sgmk/Parametrized-RAKO-Box/STL-Ready4Print/V5/midSize/midSize_V5_box.stl

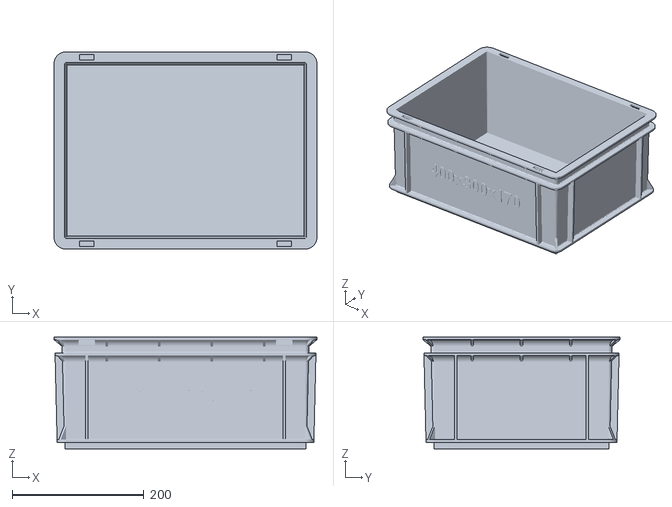
[picture p26: CAD file, 2026-09-07]
STL-Ready4Print/V5/midSize/midSize_V5_box.stl
400.0 x 300.0 x 170.0
