sgmk/Parametrized-RAKO-Box/STL-Ready4Print/V5/miniSize/miniSize_V5_lid_lower.stl

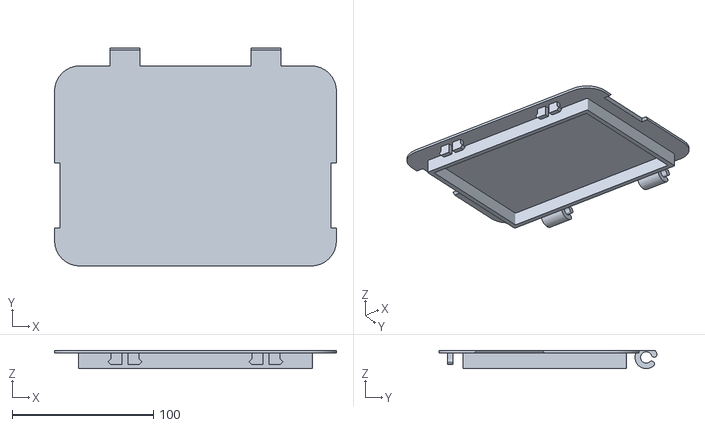
[picture p27: CAD file, 2026-09-07]
STL-Ready4Print/V5/miniSize/miniSize_V5_lid_lower.stl
200.0 x 154.6 x 13.0
