sgmk/Parametrized-RAKO-Box/STL-Ready4Print/V5/largeSize/largeSize_V5_lid_lower.stl

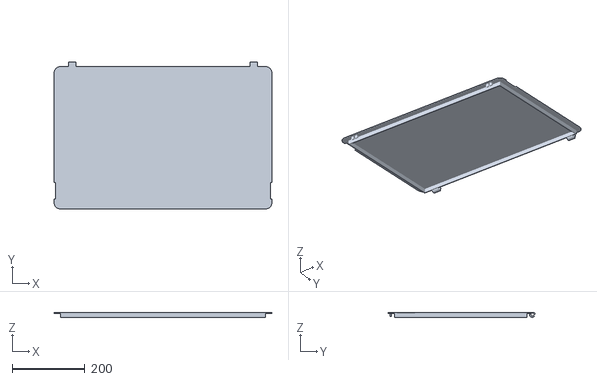
[picture p28: CAD file, 2026-09-07]
STL-Ready4Print/V5/largeSize/largeSize_V5_lid_lower.stl
600.0 x 404.6 x 13.0
