sgmk/Parametrized-RAKO-Box/STL-Ready4Print/V5/midSize/midSize_V5_lid_lower.stl

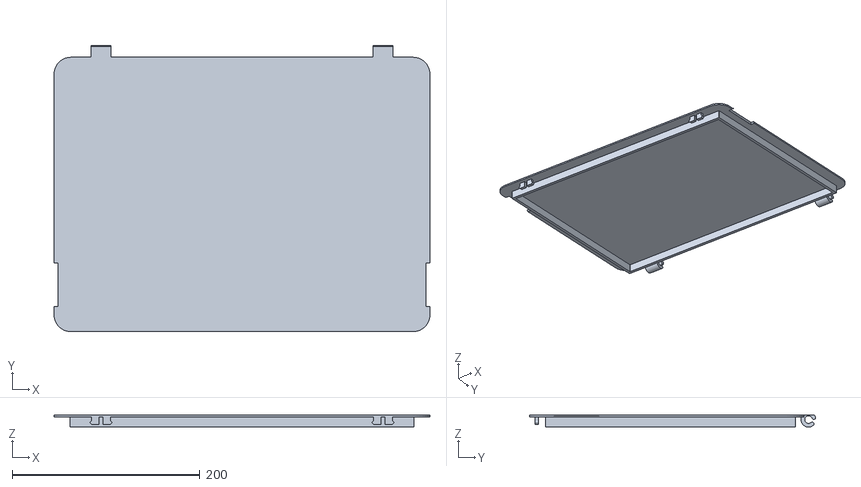
[picture p29: CAD file, 2026-09-07]
STL-Ready4Print/V5/midSize/midSize_V5_lid_lower.stl
400.0 x 304.6 x 13.0
