sgmk/Parametrized-RAKO-Box/STL-Ready4Print/V5/miniSize/miniSize_V5_lid_upper_scale0.33.stl

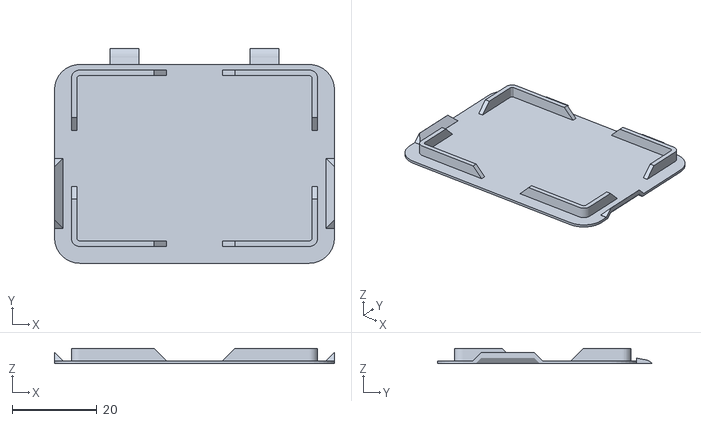
[picture p30: CAD file, 2026-09-07]
STL-Ready4Print/V5/miniSize/miniSize_V5_lid_upper_scale0.33.stl
66.0 x 50.6 x 3.63
