sgmk/Parametrized-RAKO-Box/STL-Ready4Print/V5/smallSize/smallSize_V5_box_scale0.33.stl

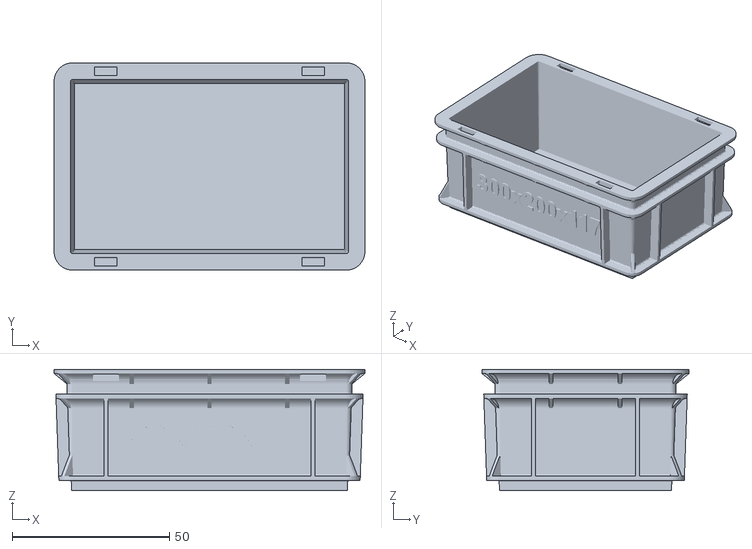
[picture p31: CAD file, 2026-09-07]
STL-Ready4Print/V5/smallSize/smallSize_V5_box_scale0.33.stl
99.0 x 66.0 x 38.6
