sgmk/Parametrized-RAKO-Box/STL-Ready4Print/V5/largeSize/largeSize_V5_lid_lower_scale0.33.stl

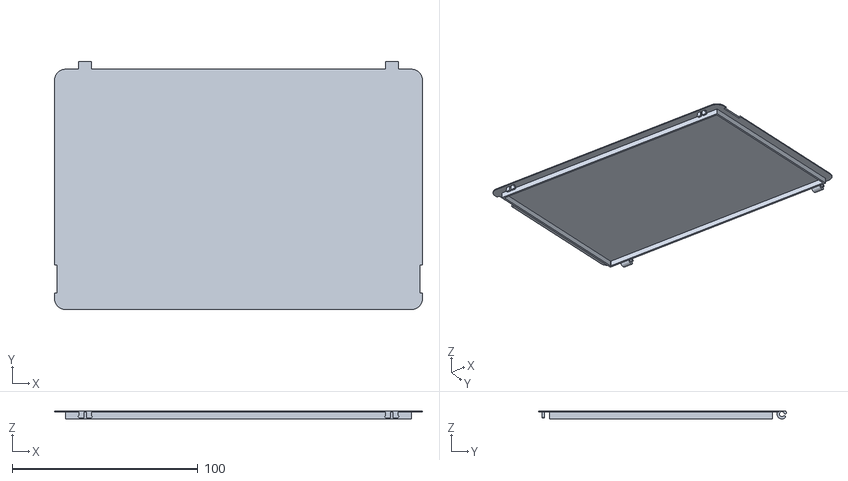
[picture p32: CAD file, 2026-09-07]
STL-Ready4Print/V5/largeSize/largeSize_V5_lid_lower_scale0.33.stl
198.0 x 133.5 x 4.29
