sgmk/Parametrized-RAKO-Box/STL-Ready4Print/V5/midSize/midSize_V5_lid_upper.stl

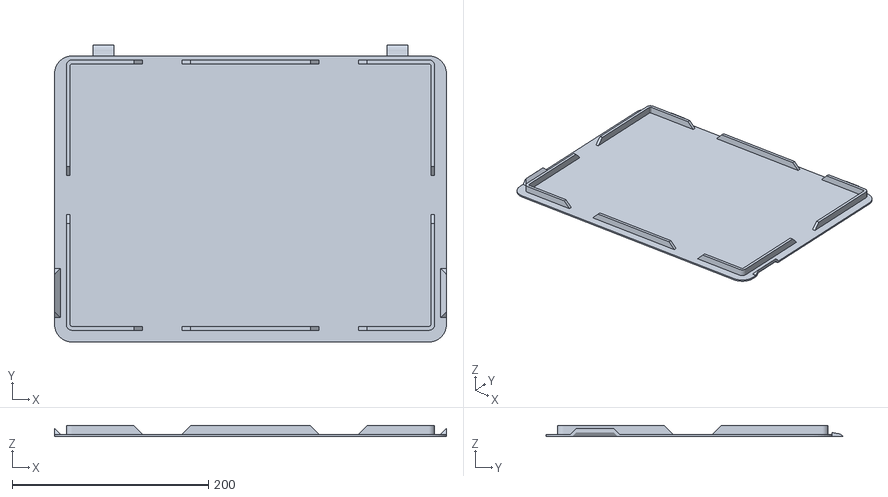
[picture p33: CAD file, 2026-09-07]
STL-Ready4Print/V5/midSize/midSize_V5_lid_upper.stl
400.0 x 303.2 x 11.0
