sgmk/Parametrized-RAKO-Box/STL-Ready4Print/V5/miniSize/miniSize_V5_lid_upper.stl

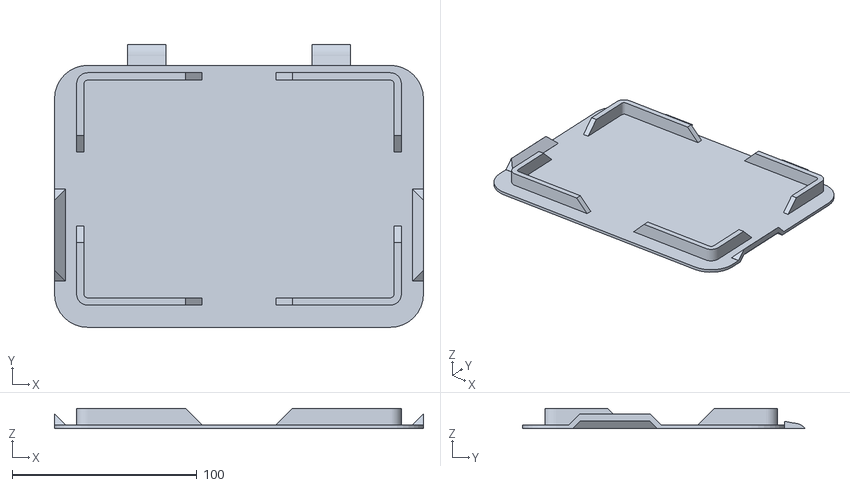
[picture p34: CAD file, 2026-09-07]
STL-Ready4Print/V5/miniSize/miniSize_V5_lid_upper.stl
200.0 x 153.2 x 11.0
