sgmk/Parametrized-RAKO-Box/STL-Ready4Print/V5/smallSize/smallSize_V5_lid_upper.stl

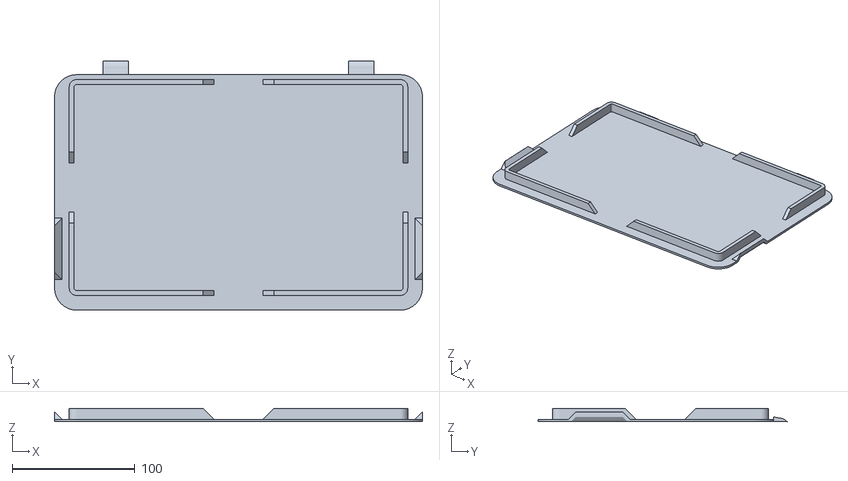
[picture p35: CAD file, 2026-09-07]
STL-Ready4Print/V5/smallSize/smallSize_V5_lid_upper.stl
300.0 x 203.2 x 11.0
